ruimartinsptl/microrato2018-pacman/Documentation/arduino-mega2560_R3-sch.jpg

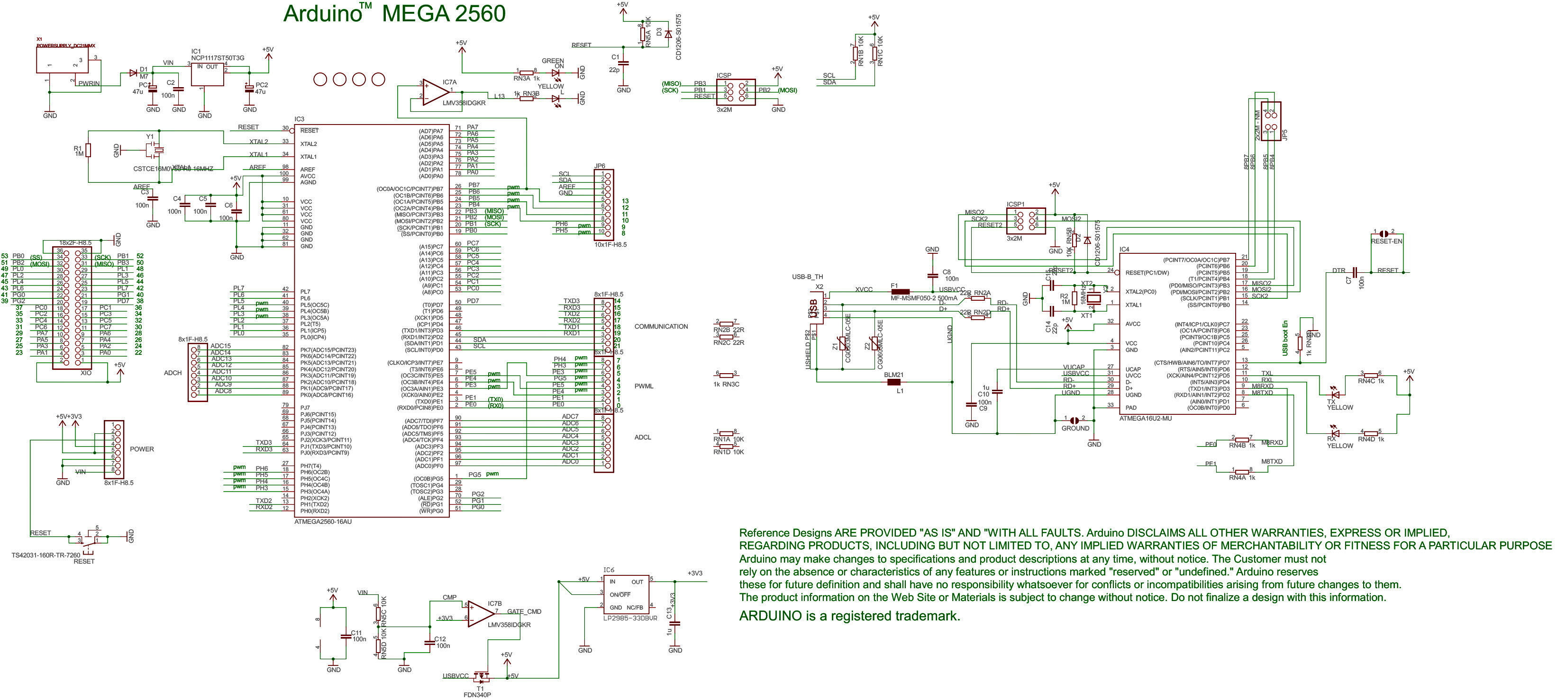
Documentation/arduino-mega2560_R3-sch.jpg
