ruimartinsptl/microrato2018-pacman/img/IMG_20180509_015023.jpg

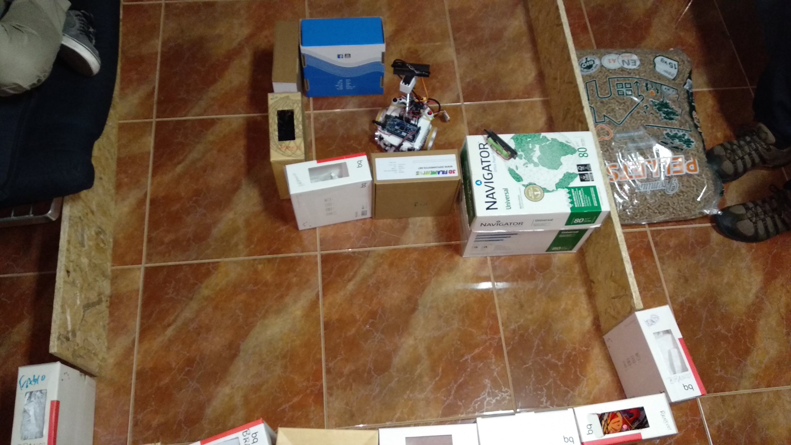
img/IMG_20180509_015023.jpg
