ruimartinsptl/microrato2018-pacman/platformio/packages/framework-arduinoespressif8266/tools/sdk/lwip2/builder/README.md

# lwIP-2 from original source

This repo offers a link layer for esp82xx-nonos-sdk-2.
The original goal is to try and use a recent lwIP version for stability reasons.
Currently lwIP-v2 is implemented, other IP stacks could be tried.

current lwIP link: [STABLE_2.0.3](http://git.savannah.nongnu.org/cgit/lwip.git/tree/?h=STABLE-2_0_3_RELEASE)

# Status

* UDP/TCP codes using lwIP-1.4 need some updates - two examples: [arduino](https://github.com/esp8266/Arduino/pull/3129) and [sming](https://github.com/SmingHub/Sming/pull/1147)
* ipv6 not tried yet
* tcp is more stable ([example1](https://github.com/esp8266/Arduino/issues/3075) and [example2](https://github.com/esp8266/Arduino/issues/2925))
* needs users / testing
* accepted pull request in [esp8266/arduino](https://github.com/esp8266/Arduino/pull/3783)
* pull request in [sming](https://github.com/SmingHub/Sming/pull/1147)
* pull request in [esp-open-sdk](https://github.com/pfalcon/esp-open-sdk/pull/271)

# Tested

* arduino NTPClient
* arduino WiFiAccessPoint
* arduino OTA
* Sming Telnet sample

# Build

makefiles are working with linux/osx/windows

get lwIP sources
```
git submodule update --init --recursive
```

optionnally tune lwIP configuration in `glue-lwip/lwipopts.h`

build & install
```
make -f Makefile.<arch> install
```

# MSS

Remember the MSS footprint: 4\*MSS bytes in RAM per tcp connection.
The lowest recommanded value is 536 which is the default here.

# How it works

Espressif binary libraries rely on their lwip implementation. The idea, as
described in this [comment](https://github.com/kadamski/esp-lwip/issues/8)
is to wrap espressif calls, and rewrite them for a new tcp implementation.

Example with lwip1.4's ethernet_input() called by espressif binary blobs
finally reaching lwip2's:

```
-- LWIP2-----------------------------------
#define ethernet_input ethernet_input_LWIP2
- lwip2's ethernet_input_LWIP2_is called
                            (/ \)
                             | |
-- glue (new side)-----------^-v-----------
                             | |
glue_ethernet_input          | |
- maps structures glue->new  |
- calls ethernet_input_LWIP2(^ v)
- maps structures new->glue    |
                             | |
-- glue (old side)-----------^-v-----------
                             | |
ethernet_input():            | |
- maps structures old->glue  | 
- calls glue_ethernet_input (^ v)
- maps structures glue->old    |
                             | |
- espressif blobs -----------^-v-----------
XXXXXXXXXXXXXXXXXXXXXXXXXXXX | | XXXXXXXXXX
wifi calls    ethernet_input(/ \) XXXXXXXXX
XXXXXXXXXXXXXXXXXXXXXXXXXXXXXXXXXXXXXXXXXXX
-------------------------------------------
```

# History

Original [cleaning and port](https://github.com/nekromant/esp8266-frankenstein/tree/master/src/contrib/lwipupdate) of espressif's patch set from lwIP-v1.4 to lwIP-v2 with references to lwIP-git-sha1

[Discussion](https://github.com/kadamski/esp-lwip/issues/8) on how further work could done

[First](https://github.com/d-a-v/esp8266-phy) version of this implementation

[Second](https://github.com/esp8266/Arduino/pull/3206) version for arduino only
