ruimartinsptl/microrato2018-pacman/pacman/src/motor_servo.h

#include <Arduino.h>
#include "pins.h"

#ifndef PACMAN_MOTOR_SERVO_H
#define PACMAN_MOTOR_SERVO_H

//void turn_on_servo(){
//    motor_servo_farol.attach(PIN_MOTOR_SERVO);
//    servo_motor_is_on = true;
//}
//
//void turn_off_servo(){
//    motor_servo_farol.detach();
//    servo_motor_is_on = false;
//}


#endif //PACMAN_MOTOR_SERVO_H
