ruimartinsptl/microrato2018-pacman/pacman/peripherals/main_sonar.cpp

// ---------------------------------------------------------------------------
// Example NewPing library sketch that does a ping about 20 times per second.
// ---------------------------------------------------------------------------

#include <NewPing.h>

#define TRIGGER_PIN  12  //8 //12  // Arduino pin tied to trigger pin on the ultrasonic sensor.
#define ECHO_PIN     13  //9 //11  // Arduino pin tied to echo pin on the ultrasonic sensor.
#define MAX_DISTANCE 200 // Maximum distance we want to ping for (in centimeters). Maximum sensor distance is rated at 400-500cm.

NewPing sonar(TRIGGER_PIN, ECHO_PIN, MAX_DISTANCE); // NewPing setup of pins and maximum distance.

void setup() {
    Serial.begin(115200); // Open serial monitor at 115200 baud to see ping results.
}


unsigned long ping_cm = 0, ping_cm_old = 0;

void loop() {
    delay(50);                     // Wait 50ms between pings (about 20 pings/sec). 29ms should be the shortest delay between pings.
//    ping_cm = sonar.ping_cm();
    ping_cm = sonar.convert_cm(sonar.ping_median());
//    ping_cm = sonar.ping_median();

    Serial.println(ping_cm);
//    if (ping_cm_old != ping_cm) {
//        Serial.println(ping_cm);
//        ping_cm_old = ping_cm;
//    }
//    graph(sonar.ping_cm(), 0, 0); // Send ping, get distance in cm and print result (0 = outside set distance range)
}
